stonedDiscord/servicetastatur/firmware/src/hd44780.h

#define HD44780_CMD_CLEAR           0x01

#define HD44780_CMD_HOME            0x02

#define HD44780_CMD_ENTRY_MODE      0x04
#define HD44780_ENTRY_LTR           0x02
#define HD44780_ENTRY_RTL           0x00
#define HD44780_ENTRY_SHIFT         0x01

#define HD44780_CMD_DISPLAY_CTRL    0x08
#define HD44780_DISPLAY_ON          0x04
#define HD44780_DISPLAY_OFF         0x00
#define HD44780_DISPLAY_CURSOR_ON   0x02
#define HD44780_DISPLAY_CURSOR_OFF  0x00
#define HD44780_DISPLAY_BLINK_ON    0x01
#define HD44780_DISPLAY_BLINK_OFF   0x00

#define HD44780_CMD_CURSOR_SHIFT    0x10
#define HD44780_SHIFT_DISPLAY       0x08
#define HD44780_SHIFT_CURSOR        0x00
#define HD44780_SHIFT_RIGHT         0x04
#define HD44780_SHIFT_LEFT          0x00

#define HD44780_CMD_FUNCTION_SET    0x20
#define HD44780_FUNCTION_8BIT       0x10
#define HD44780_FUNCTION_4BIT       0x00
#define HD44780_FUNCTION_2LINE      0x08
#define HD44780_FUNCTION_1LINE      0x00
#define HD44780_FUNCTION_5X10DOTS   0x04
#define HD44780_FUNCTION_5X7DOTS    0x00

#define HD44780_CMD_SET_CGRAM_ADDR  0x40

#define HD44780_CMD_SET_DDRAM_ADDR  0x80

#define HD44780_BUSY                0x80

#define HD44780_LINE1_ADDR          0x00
#define HD44780_LINE2_ADDR          0x40
